sparkfun/SparkFun_Thing_Plus_RA6M5/docs/resources.md

---
icon: material/book-open-page-variant
---

## Product Resources

- :sfe-logo: [Product Page](https://www.sparkfun.com/products/24243)
- :material-folder-cog: Design Files:
	- :fontawesome-solid-file-pdf: [Schematic](./assets/board_files/schematic.pdf)
	- :fontawesome-solid-file-pdf: [Board Dimensions](./assets/board_files/dimensions.pdf)
	- :material-folder-zip: [Eagle Files](./assets/board_files/eagle_files.zip)
- :fontawesome-solid-file-pdf: [Graphical Datasheet](./assets/board_files/graphical_datasheet.pdf)
- :simple-arduino: [Renesas Arduino Core](https://github.com/arduino/ArduinoCore-renesas)
- :simple-arduino: Arduino Libraries:
	- [FastLED Arduino library](https://github.com/FastLED/FastLED/)
	- [SparkFun MAX1704x Fuel Gauge Arduino library](https://github.com/sparkfun/SparkFun_MAX1704x_Fuel_Gauge_Arduino_Library)
	- :material-folder-zip: [CodeLess Arduino Library](./assets/CodelessBLE.zip) *(unofficial - `CodeLess.zip`)*
- :material-youtube: [SFE Product Showcase](https://www.youtube.com/watch?v=A9NTdowiY_o)
- :material-github: [Hardware Repo](https://github.com/sparkfun/SparkFun_Thing_Plus_RA6M5)

### :sfe-logo: Additional Resources

- :material-folder-multiple: Component Documentation:

	<div class="grid cards" markdown>

	-   **RA6M5 Microcontroller**

		- :fontawesome-solid-file-pdf: [Datasheet](https://www.renesas.com/us/en/document/dst/ra6m5-group-datasheet?r=1493931)
		- :fontawesome-solid-file-pdf: [User Manual](https://www.renesas.com/us/en/document/man/ra6m5-group-users-manual-hardware?r=1493931)

	-   **DA14531MOD Bluetooth Module**

		- :fontawesome-solid-file-pdf: [Datasheet](https://www.renesas.com/us/en/document/dst/da14531-module-datasheet)
		- :material-web: [Codeless™ User Manual](https://lpccs-docs.renesas.com/UM-140-DA145x-CodeLess/index.html)

	-   **Peripherals Devices**

		- :fontawesome-solid-file-pdf: [MAX17048 Battery Fuel Gauge](./assets/component_documentation/MAX17048.pdf)
		- :fontawesome-solid-file-pdf: [WS2812 RGB LED](./assets/component_documentation/WS2812C-2020.pdf)
		- :fontawesome-solid-file-pdf: [MX25L12833F QSPI FLash](./assets/component_documentation/MX25L12833F.pdf)

	-   **Power Components**

		- :fontawesome-solid-file-pdf: [RT9080 LDO Voltage Regulator](./assets/component_documentation/RT9080.pdf)
		- :fontawesome-solid-file-pdf: [LM66200 Ideal Diode Switch](./assets/component_documentation/LM66200.pdf)
		- :fontawesome-solid-file-pdf: [MCP73831 Charge Controller](./assets/component_documentation/MCP73831.pdf)

	</div>

- [Thing Plus Comparison Guide](https://www.sparkfun.com/thing_plus)
- [Qwiic Information Page](https://www.sparkfun.com/qwiic)
- :material-account-supervisor: [SparkFun Technical Assistance](https://www.sparkfun.com/technical_assistance)

### 🏭&nbsp;Manufacturer's Resources
Renesas also provides great resources for the RA6M5 and DA14531MOD:

- [SmartBond™ Flash Programmer](https://lpccs-docs.renesas.com/um-b-138/introduction.html)
- :material-help-box: [RenesasRulz Forum](https://renesasrulz.com/)

<div class="grid cards" markdown>

-   [RA6M5 Product Page](https://www.renesas.com/us/en/products/microcontrollers-microprocessors/ra-cortex-m-mcus/ra6m5-200mhz-arm-cortex-m33-trustzone-highest-integration-ethernet-and-can-f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)

	---

	- [Documentation](https://www.renesas.com/us/en/products/microcontrollers-microprocessors/ra-cortex-m-mcus/ra6m5-200mhz-arm-cortex-m33-trustzone-highest-integration-ethernet-and-can-f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)
		- [RA6M5 Group Datasheet](https://www.renesas.com/us/en/document/dst/ra6m5-group-datasheet?r=1493931)
		- [RA6M5 Group User Manual: Hardware](https://www.renesas.com/us/en/document/man/ra6m5-group-users-manual-hardware?r=1493931)
	- [Software and Tools](https://www.renesas.com/us/en/products/microcontrollers-microprocessors/ra-cortex-m-mcus/ra6m5-200mhz-arm-cortex-m33-trustzone-highest-integration-ethernet-and-can-f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)

-   [DA14531MOD Product Page](https://www.renesas.com/us/en/products/wireless-connectivity/bluetooth-low-energy/da14531mod-smartbond-tiny-bluetooth-low-energy-module)

	---

	- [Documentation](https://www.renesas.com/us/en/products/wireless-connectivity/bluetooth-low-energy/da14531mod-smartbond-tiny-bluetooth-low-energy-module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)
		- [DA14531MOD Datasheet](https://www.renesas.com/us/en/document/dst/da14531-module-datasheet)
	- [Software and Tools](https://www.renesas.com/us/en/products/wireless-connectivity/bluetooth-low-energy/da14531mod-smartbond-tiny-bluetooth-low-energy-module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)
		- [DA145`XX` CodeLess™ User Manual](https://lpccs-docs.renesas.com/UM-140-DA145x-CodeLess/index.html)
		- [SmartBond™ - CodeLess™ AT commands](https://www.renesas.com/us/en/software-tool/smartbond-codeless-commands)
		- [DA1453`x` SW Platform Reference Manual](https://lpccs-docs.renesas.com/UM-B-119_DA14585-DA14531_SW_Platform_Reference/index.html)
	- Tutorials:
		- [Tutorial - Sleep Modes](https://lpccs-docs.renesas.com/tutorial_da145xx_sleep_modes/index.html)
		- [Tutorial - Peripheral Drivers *(Dialog SDK 6.0.`x`)*](https://lpccs-docs.renesas.com/da145xx_tutorial_sdk6_peripherals/introduction.html)
		- [Tutorial - Debugging *(Dialog SDK 6.0.`x`)*](https://lpccs-docs.renesas.com/tutorial_da145xx_debugging_techniques/index.html)
		- [Tutorial - BLE Serial Port Service](https://lpccs-docs.renesas.com/Tutorial_DA145xx_DSPS_Getting_Started/index.html)
		- [Tutorial - BLE Advertising](https://lpccs-docs.renesas.com/DA145xx_Advertising_Tutorial/index.html)
		- [Tutorial - Create a Custom GATT Profile](https://lpccs-docs.renesas.com/tutorial-custom-profile-DA145xx/index.html)
		- :material-github: [SDK 6.0.`x` BLE Examples](https://github.com/dialog-semiconductor/BLE_SDK6_examples)

</div>

<article style="text-align: center;" markdown>
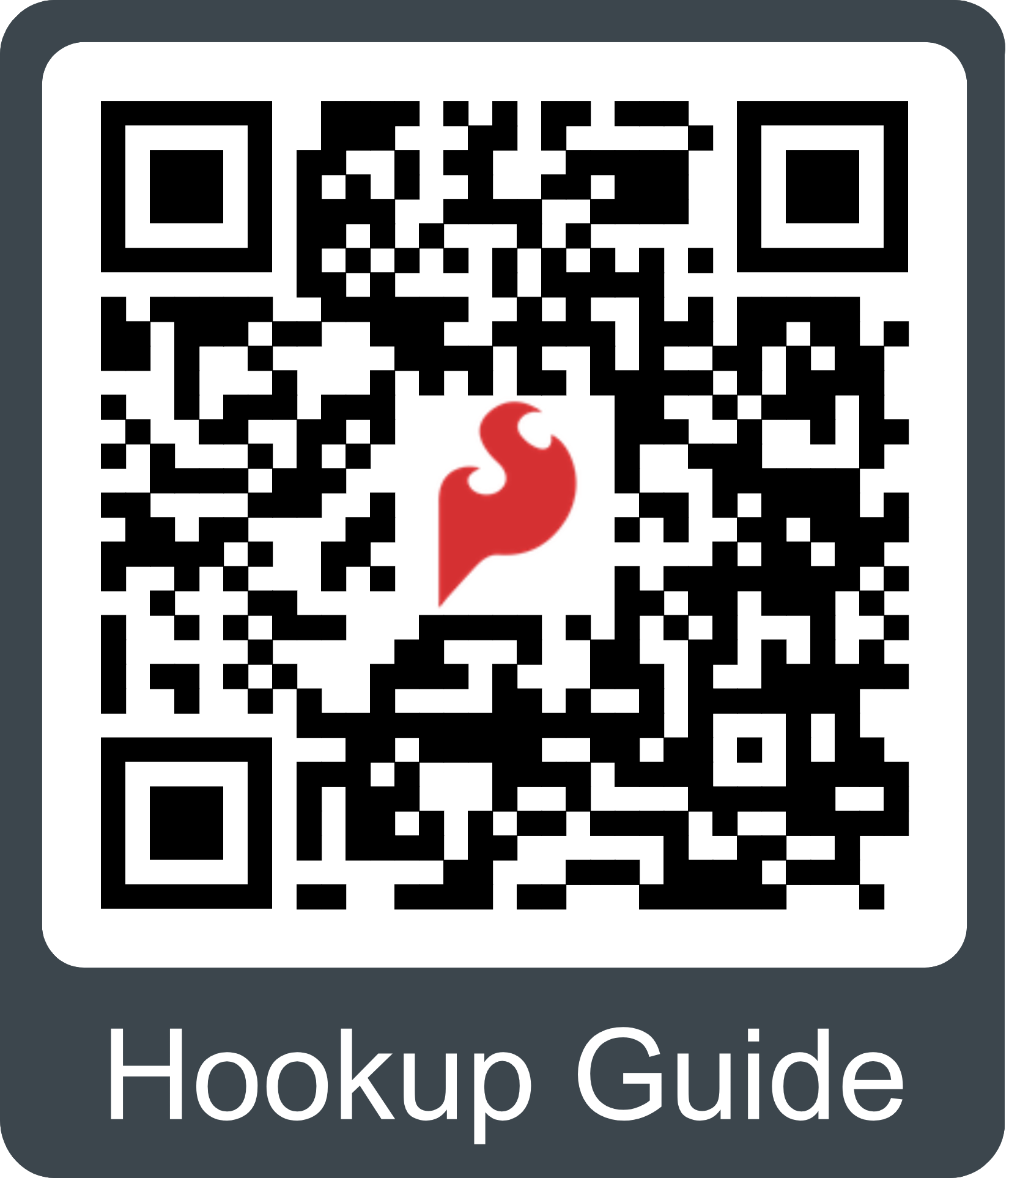
[picture p45: docs/assets/img/qr_code/hookup_guide.png]
QR code to the hookup guide

</article>
