sparkfun/SparkFun_Thing_Plus_RA6M5/docs/github/contribute.md

# Contribute: Make an Augmentation!
Spot an improvement opportunity? Feel free to contribute to our open-source design and documentation. 

## :material-file-document-multiple:&nbsp;Improve our Documentation
All of this documentation can be modified by you! Please help us make it better.

* These pages are contained in the [`docs` folder](https://github.com/sparkfun/SparkFun_Thing_Plus_RA6M5/tree/main/docs) of the [SparkFun RA6M5 Thing Plus repository](https://github.com/sparkfun/SparkFun_Thing_Plus_RA6M5).

<!-- ### :material-source-pull:&nbsp;Submit a Correction -->
### Submit a Correction

1. With a GitHub account, [fork this repository](https://github.com/sparkfun/SparkFun_Thing_Plus_RA6M5/fork).
2. Add your corrections or improvements to the markdown file.
3. File a pull request with your changes, and enjoy making the ~~words~~ ~~worlds~~ world a better place.
	* Once received, the documentation specialist will automatically be notified.
	* We will review your suggested improvements to make sure they are correct and fit within our documentation standards.

## :material-cog:&nbsp;Improve our Hardware Design
All of our designs are open-source! Please help us make it better.

* Our board design files are contained in the [`Hardware` folder](https://github.com/sparkfun/SparkFun_Thing_Plus_RA6M5/tree/main/Hardware) of the [SparkFun RA6M5 Thing Plus repository](https://github.com/sparkfun/SparkFun_Thing_Plus_RA6M5).

<!-- ### :material-source-pull:&nbsp;Submit a Design Enhancement -->
### Submit a Design Enhancement

1. With a GitHub account, [fork this repository](https://github.com/sparkfun/SparkFun_Thing_Plus_RA6M5/fork).
2. Add your design augmentation(s)
3. File a pull request with your changes, and enjoy making the ~~words~~ ~~worlds~~ world a better place.
	1. Once received, the engineer in charge of the original design will automatically be notified.
	2. We will review your suggested improvement(s) to verify that they are within our board design standards and meet our product design requirements.
	3. If approved, we will flag these changes for our next board revision. Congrats! 🍻

		!!! info
			Even if your suggestion is accepted, these changes may not be immediately available for purchase. We may have to cycle through our current product inventory first.

## Contributors&nbsp;:clap:
Let's provide some recognition to the contributors for this project!

GitHub Contributors Image
<br>
