sparkfun/SparkFun_Thing_Plus_RA6M5/docs/assets/board_files/dimensions2.png

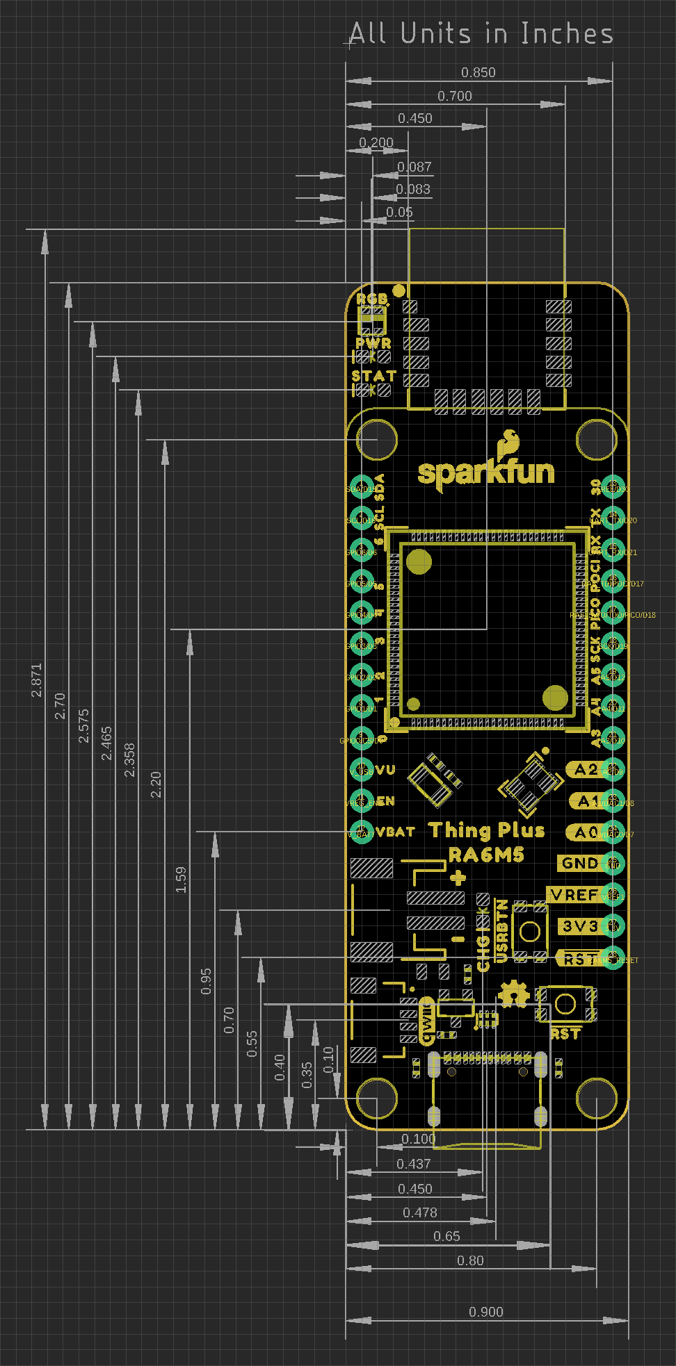
docs/assets/board_files/dimensions2.png
