sparkfun/SparkFun_Thing_Plus_RA6M5/docs/assets/img/thumbnail.jpg

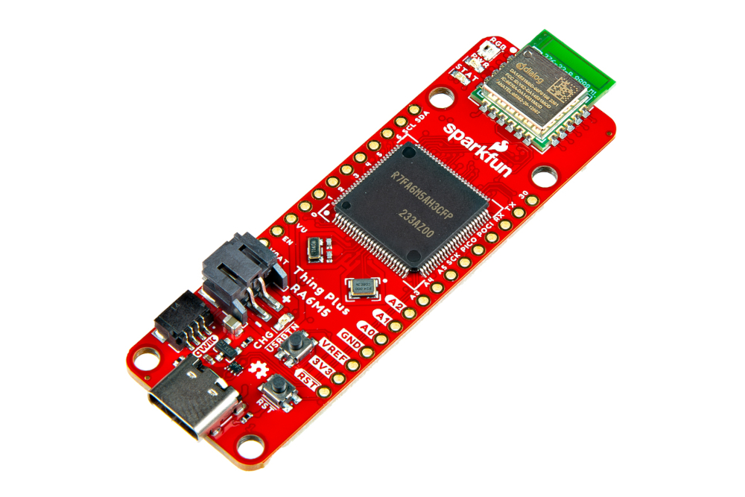
docs/assets/img/thumbnail.jpg
