sparkfun/SparkFun_Thing_Plus_RA6M5/docs/assets/img/hookup_guide/example-DAC_oscilloscope2.png

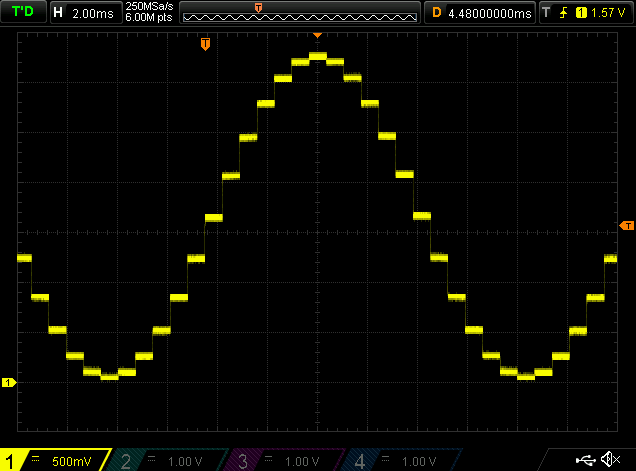
docs/assets/img/hookup_guide/example-DAC_oscilloscope2.png
