sparkfun/SparkFun_Thing_Plus_RA6M5/docs/assets/img/hookup_guide/pins-i2s.png

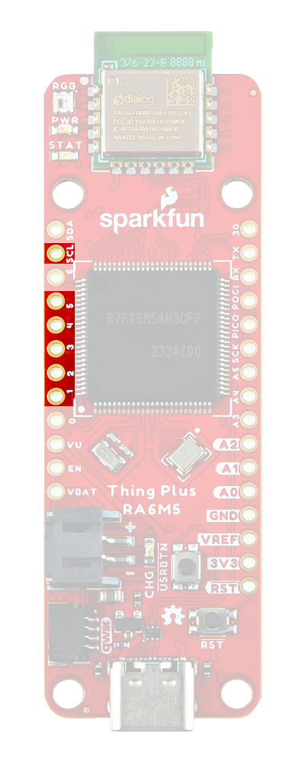
docs/assets/img/hookup_guide/pins-i2s.png
