sparkfun/SparkFun_Thing_Plus_RA6M5/docs/assets/img/hookup_guide/RA6M5_Thing_Plus-top.png

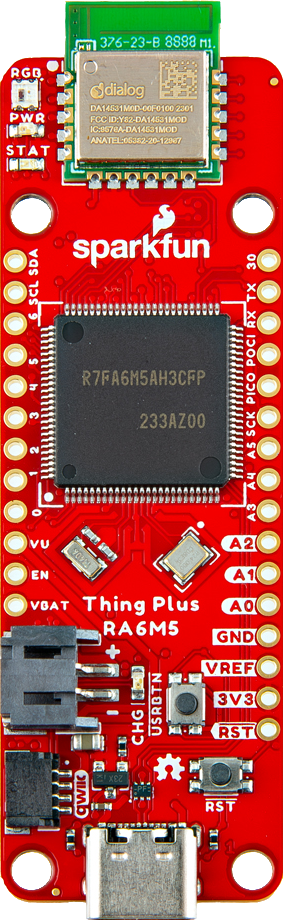
docs/assets/img/hookup_guide/RA6M5_Thing_Plus-top.png
